igor-mbs/OpenLogger/pictures/IMG_1907.JPG

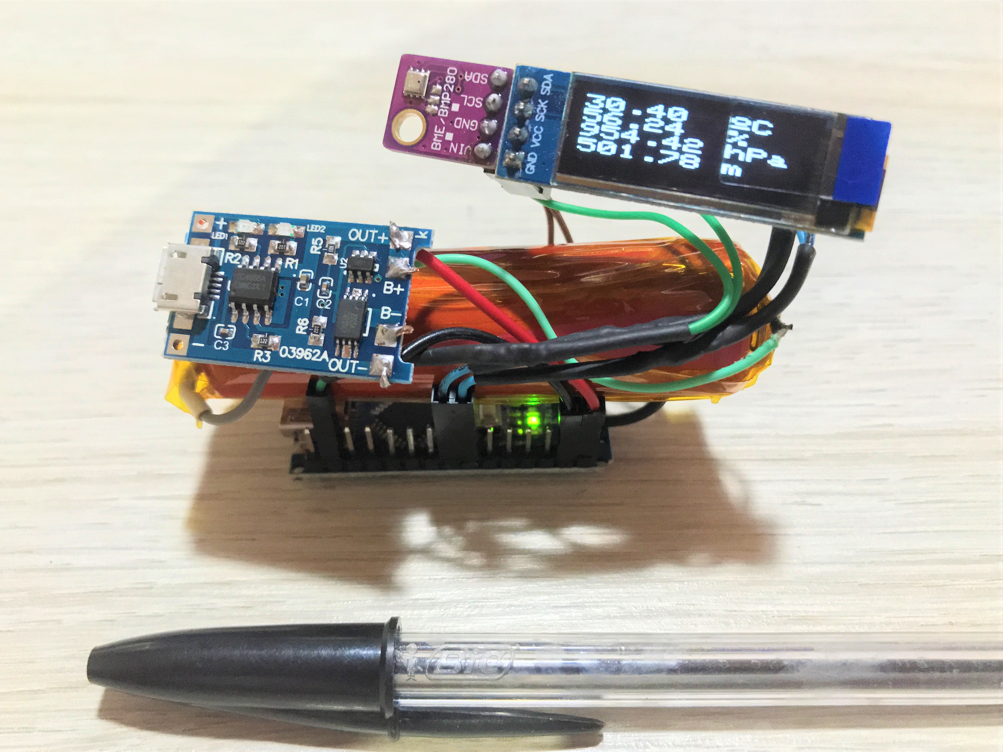
pictures/IMG_1907.JPG
